gruvin/gruvin9x/wiki/Recognition.md

# Financial Contributors / Donators #

A number of people have contributed financially to the gruvin9x project by way of cash donations, consignment stock cost assistance and more.

The table below lists the first names (or initials) and country of financial contributors to date, in approximate chronological order.

## The gruvin9x Hall of (Financial) Recognition ##

| **Name** | **Country** |
|:---|:---|
| Keith | New Zealand |
| Cameron | United Kingdom |
| Jim | United States |
| Leo | Switzerland |
| Romolo | Italy |
| Brano | Canada |
| James | Canada |
| Rick | CA, USA |
| Tad L | MI, USA |

Many others have contributed their time or simply spread the word to the friends and colleagues, including many we have never heard from directly. To each and every one of you, please accept this token note of gratitude.
