gruvin/gruvin9x/wiki/About.attach/g9x-open-power.gif

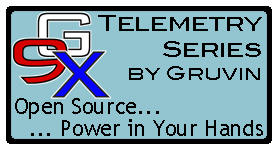
wiki/About.attach/g9x-open-power.gif
