gruvin/gruvin9x/wiki/About.attach/gruvin9x-lcd.jpg

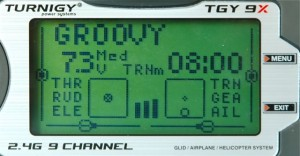
wiki/About.attach/gruvin9x-lcd.jpg
