gruvin/gruvin9x/wiki/Features.attach/drexpo_01.png

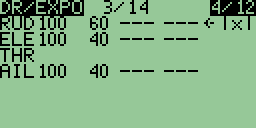
wiki/Features.attach/drexpo_01.png
