gruvin/gruvin9x/wiki/Features.attach/drexpo_02.png

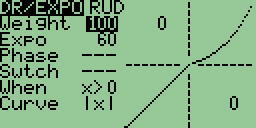
wiki/Features.attach/drexpo_02.png
