gruvin/gruvin9x/wiki/Features.attach/drexpo_04.png

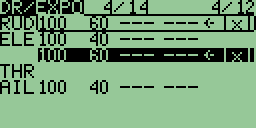
wiki/Features.attach/drexpo_04.png
