gruvin/gruvin9x/wiki/Features.attach/flightphases_01.png

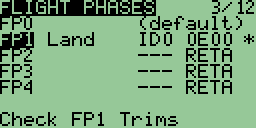
wiki/Features.attach/flightphases_01.png
