gruvin/gruvin9x/wiki/Features.attach/mainscreen_01.jpg

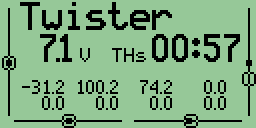
wiki/Features.attach/mainscreen_01.jpg
