gruvin/gruvin9x/wiki/Features.attach/mainscreen_02.jpg

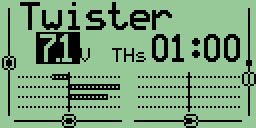
wiki/Features.attach/mainscreen_02.jpg
