gruvin/gruvin9x/wiki/Features.attach/mainscreen_04.jpg

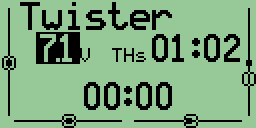
wiki/Features.attach/mainscreen_04.jpg
