gruvin/gruvin9x/wiki/Features.attach/modelsel_01.png

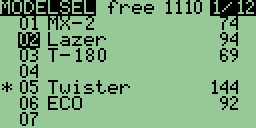
wiki/Features.attach/modelsel_01.png
