gruvin/gruvin9x/wiki/Features.attach/modelsel_02.png

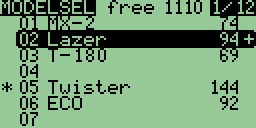
wiki/Features.attach/modelsel_02.png
