gruvin/gruvin9x/wiki/Features.attach/snapshot_01.png

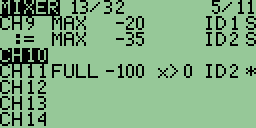
wiki/Features.attach/snapshot_01.png
