gruvin/gruvin9x/wiki/FrSky.attach/no-data-ani.gif

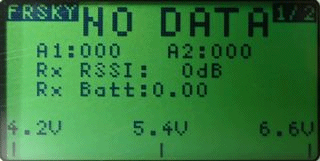
wiki/FrSky.attach/no-data-ani.gif
