gruvin/gruvin9x/wiki/PCB.attach/pcb_v3.2_3d_top.png

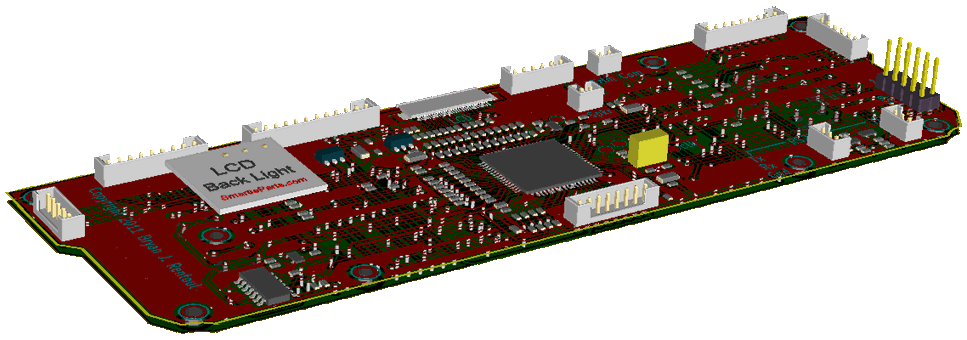
wiki/PCB.attach/pcb_v3.2_3d_top.png
