gruvin/gruvin9x/wiki/Progress.attach/FrSky RX Voltage.jpg

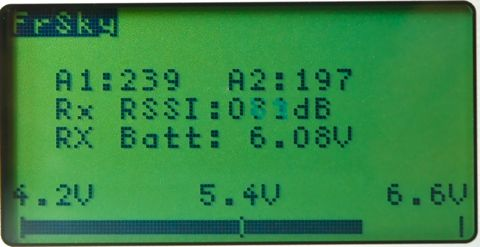
wiki/Progress.attach/FrSky RX Voltage.jpg
