gruvin/gruvin9x/archive/pcb-v4.1a-frozen/assembly/9xLABEL.pdf

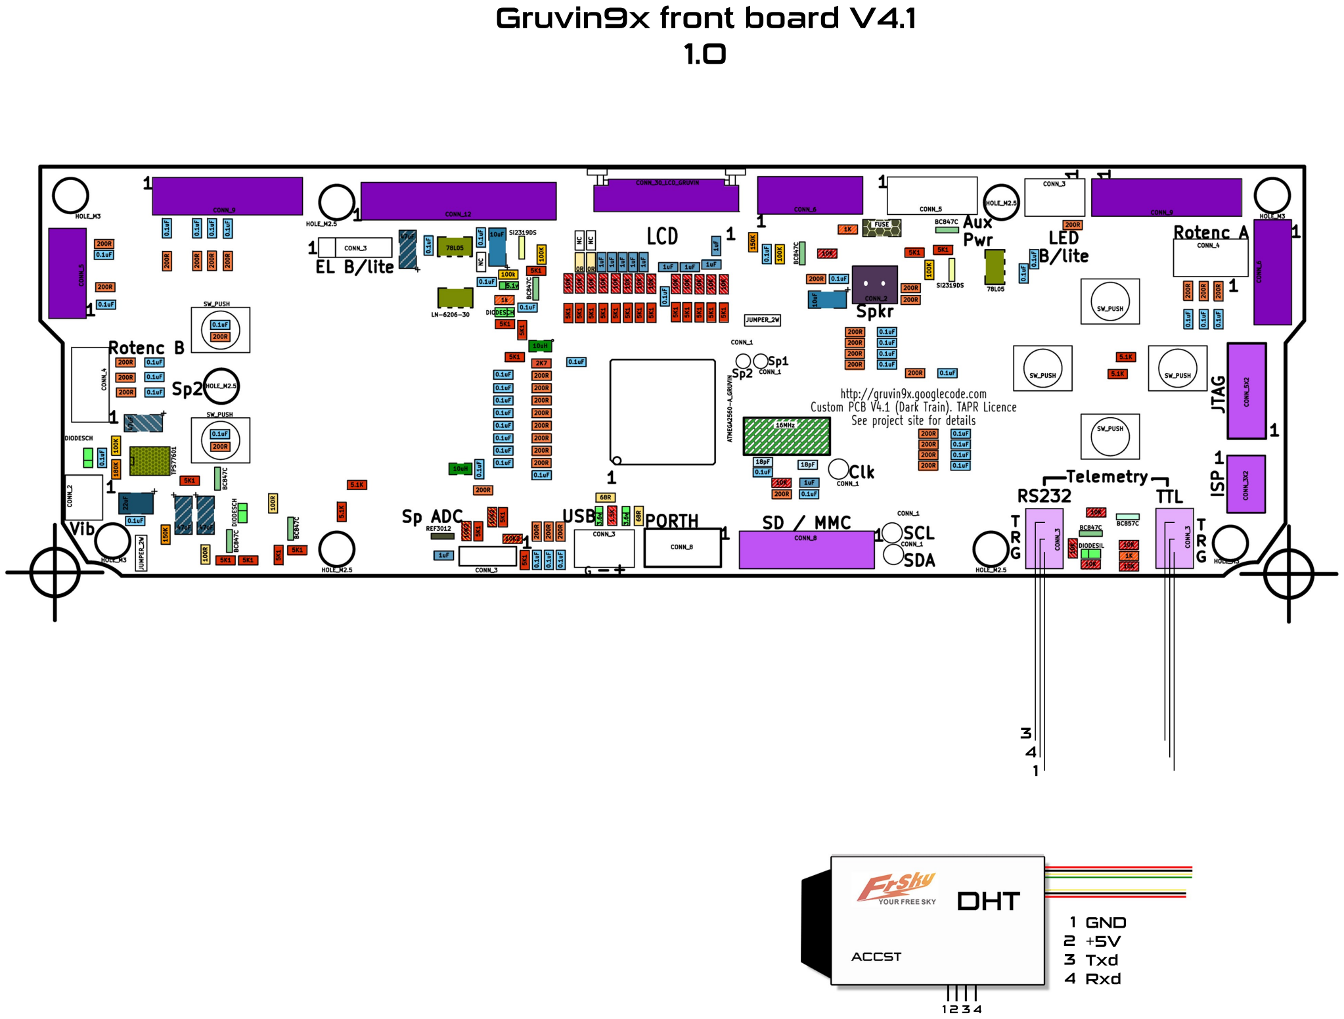
[picture p96: page 1]

Gruvin9x front board V4.1
1.0

1 2 3 4

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
