gruvin/gruvin9x/wiki/V41FAQ.attach/rot-enc-inside1.jpg

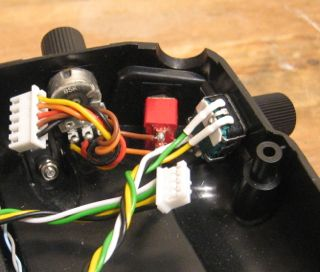
wiki/V41FAQ.attach/rot-enc-inside1.jpg
