gruvin/gruvin9x/archive/pcb-v4.1a-frozen/assembly/gruvin9x-SilkS_Front.pdf

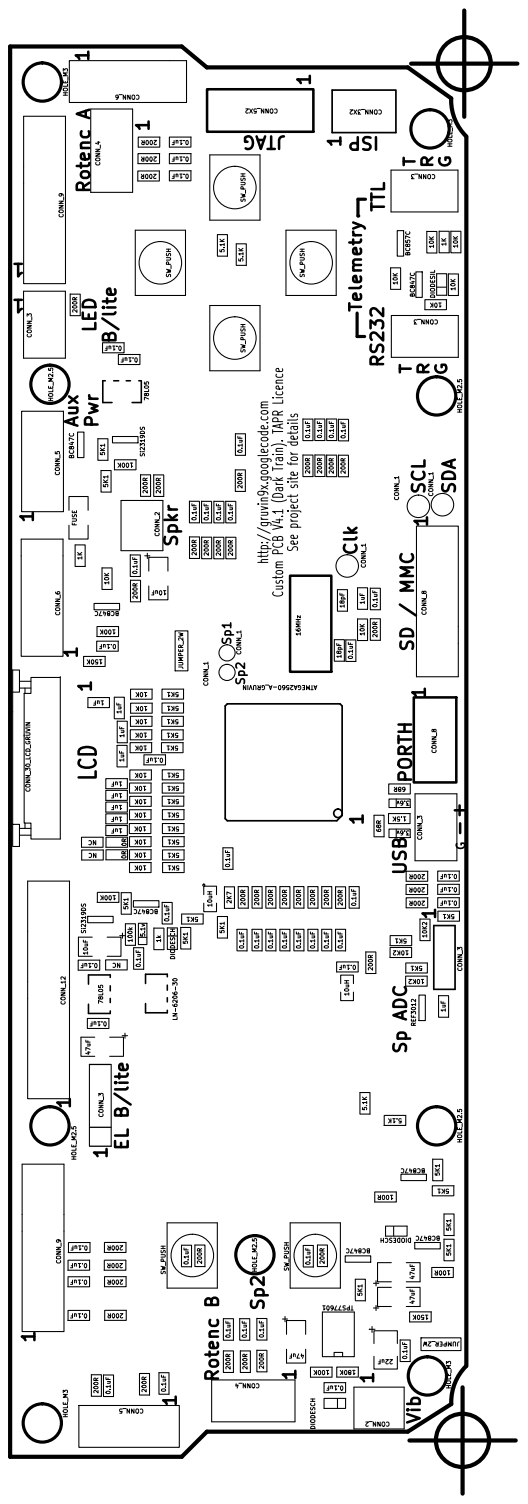
[picture p111: page 1]
