gruvin/gruvin9x/archive/pcb-v4.2-frozen/assembly/gruvin9x-v4.2-part-placement.pdf

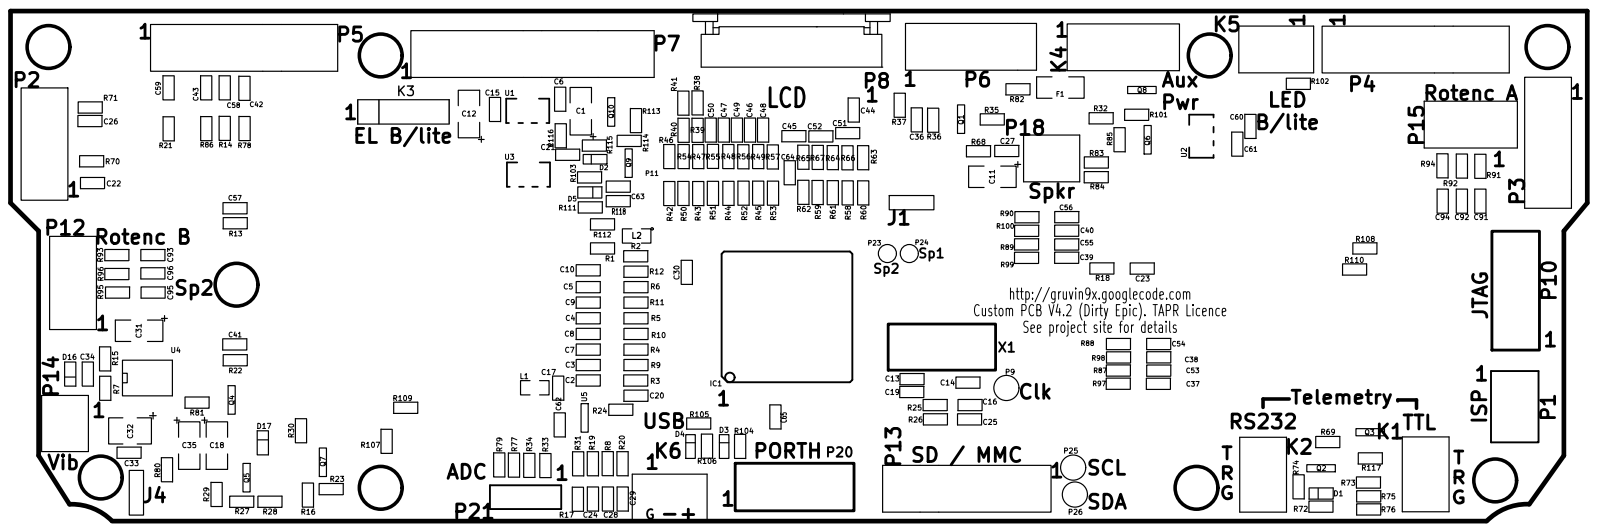
[picture p112: page 1]
