gruvin/gruvin9x/archive/pcb-v4.2-frozen/assembly/gruvin9x-v4.2-schematic.pdf

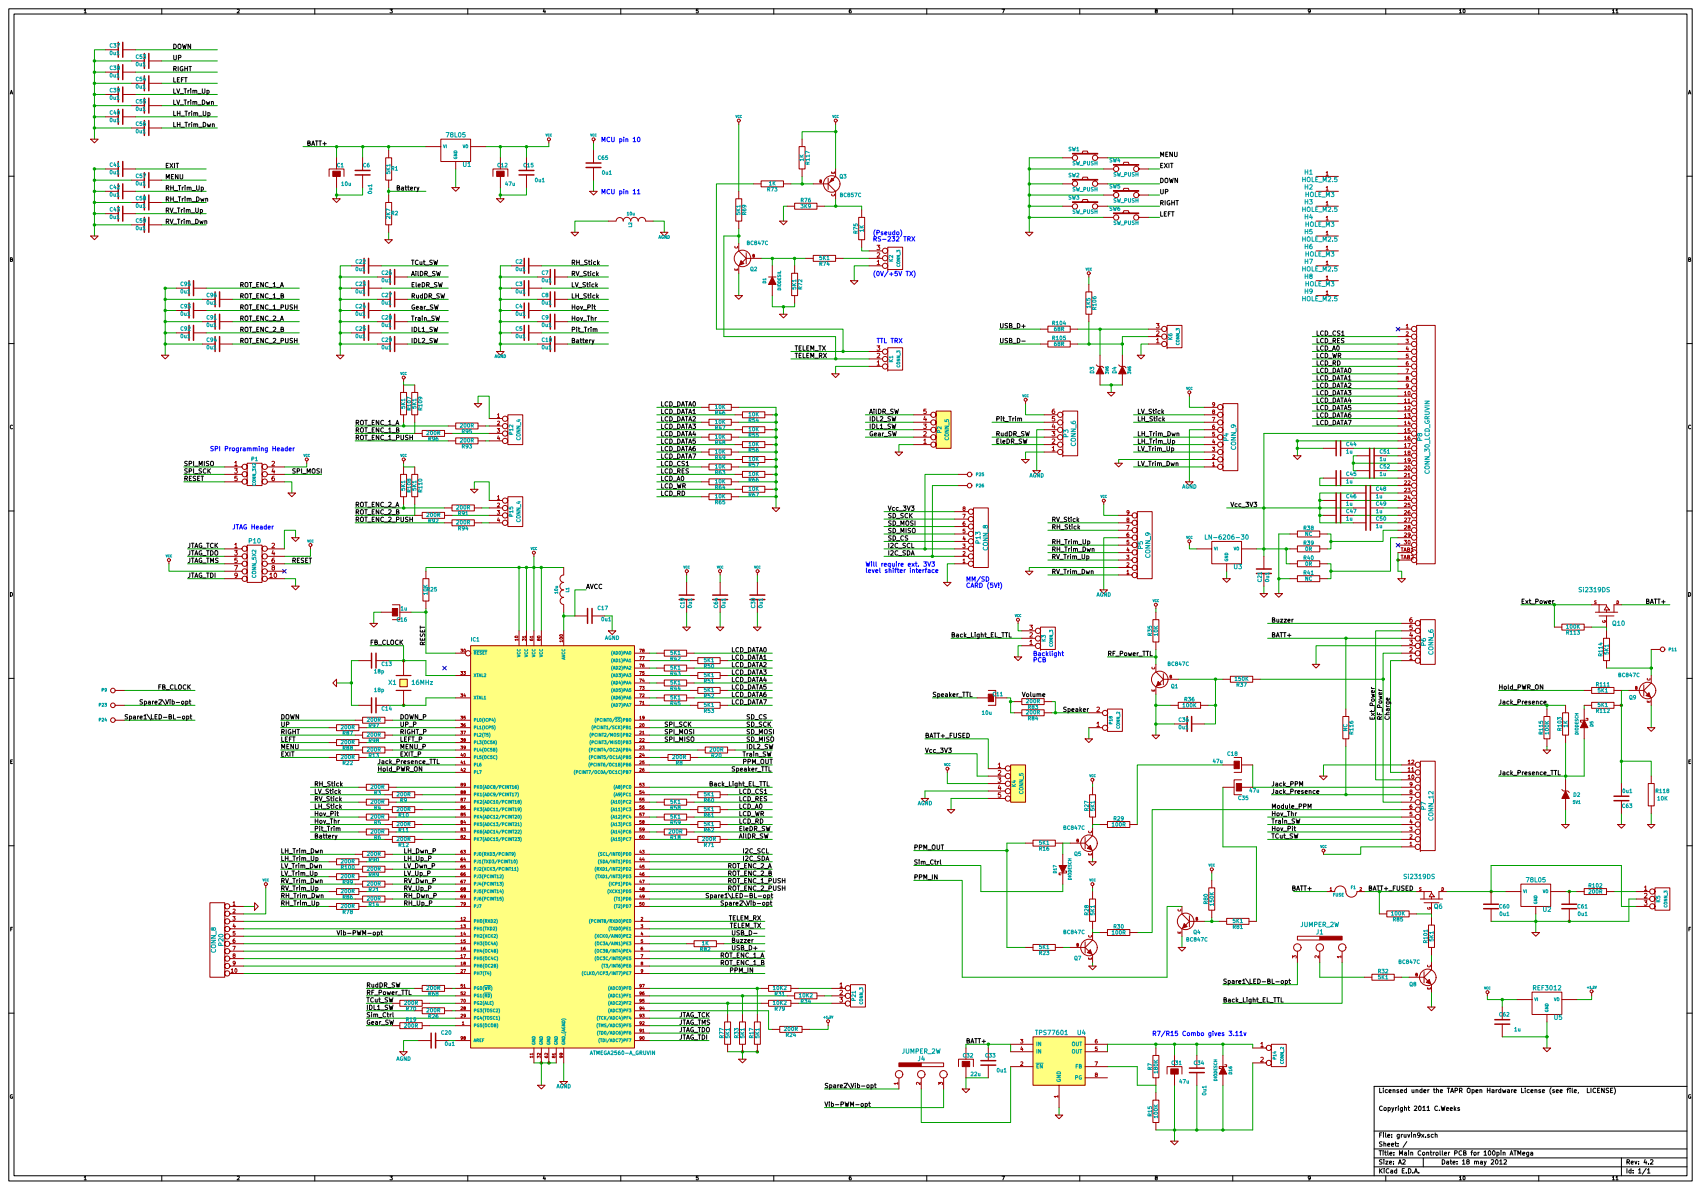
[picture p113: page 1]
