gruvin/gruvin9x/archive/pcb-v4.1a-frozen/assembly/sdcard_uk-SilkS_Front.pdf

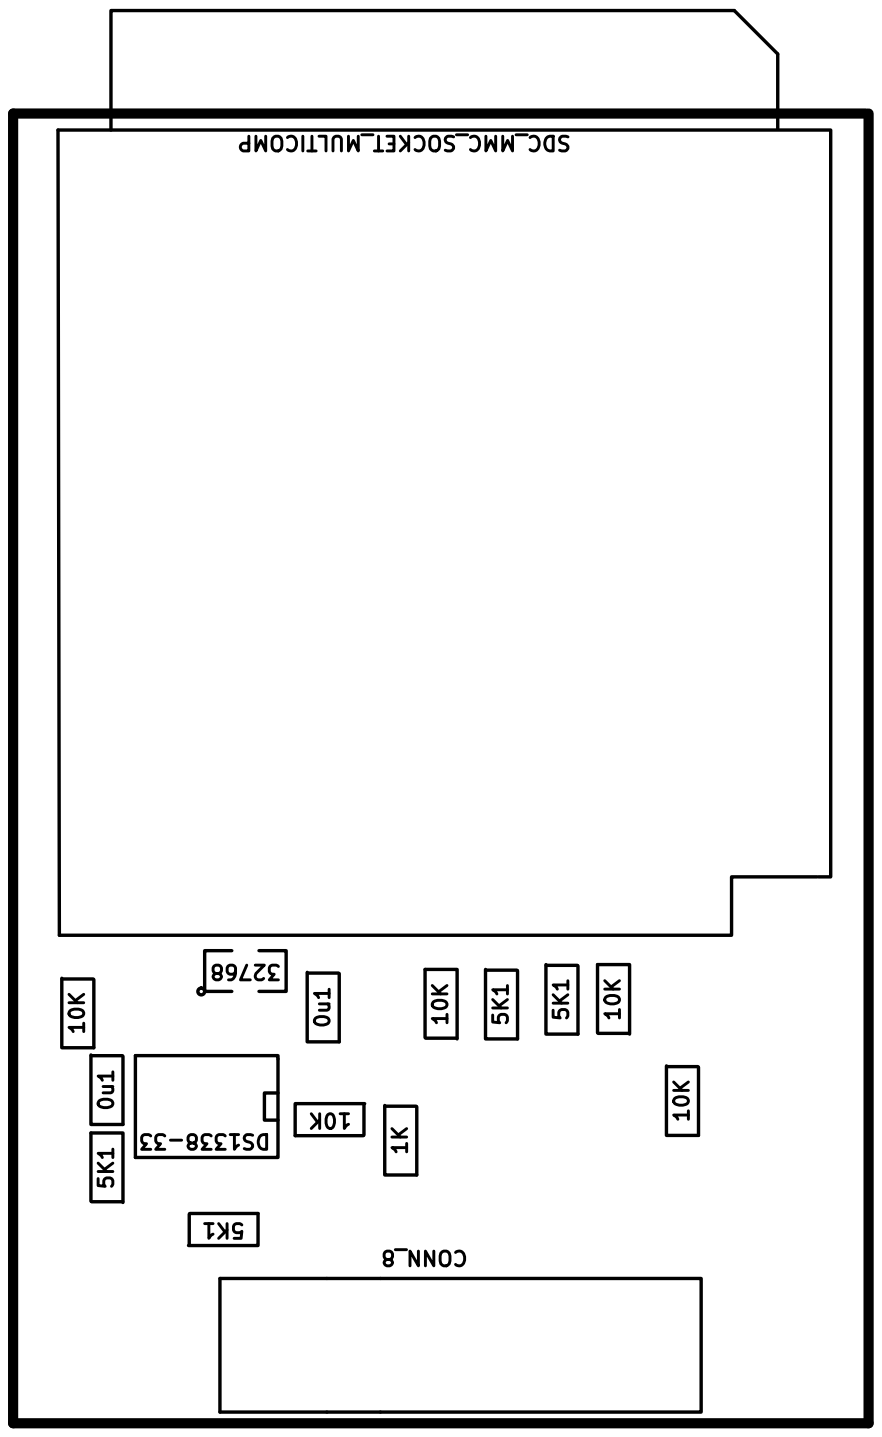
[picture p114: page 1]
