gruvin/gruvin9x/archive/pcb-v4.0-frozen/assembly/gruvin9x-SilkS_Front.pdf

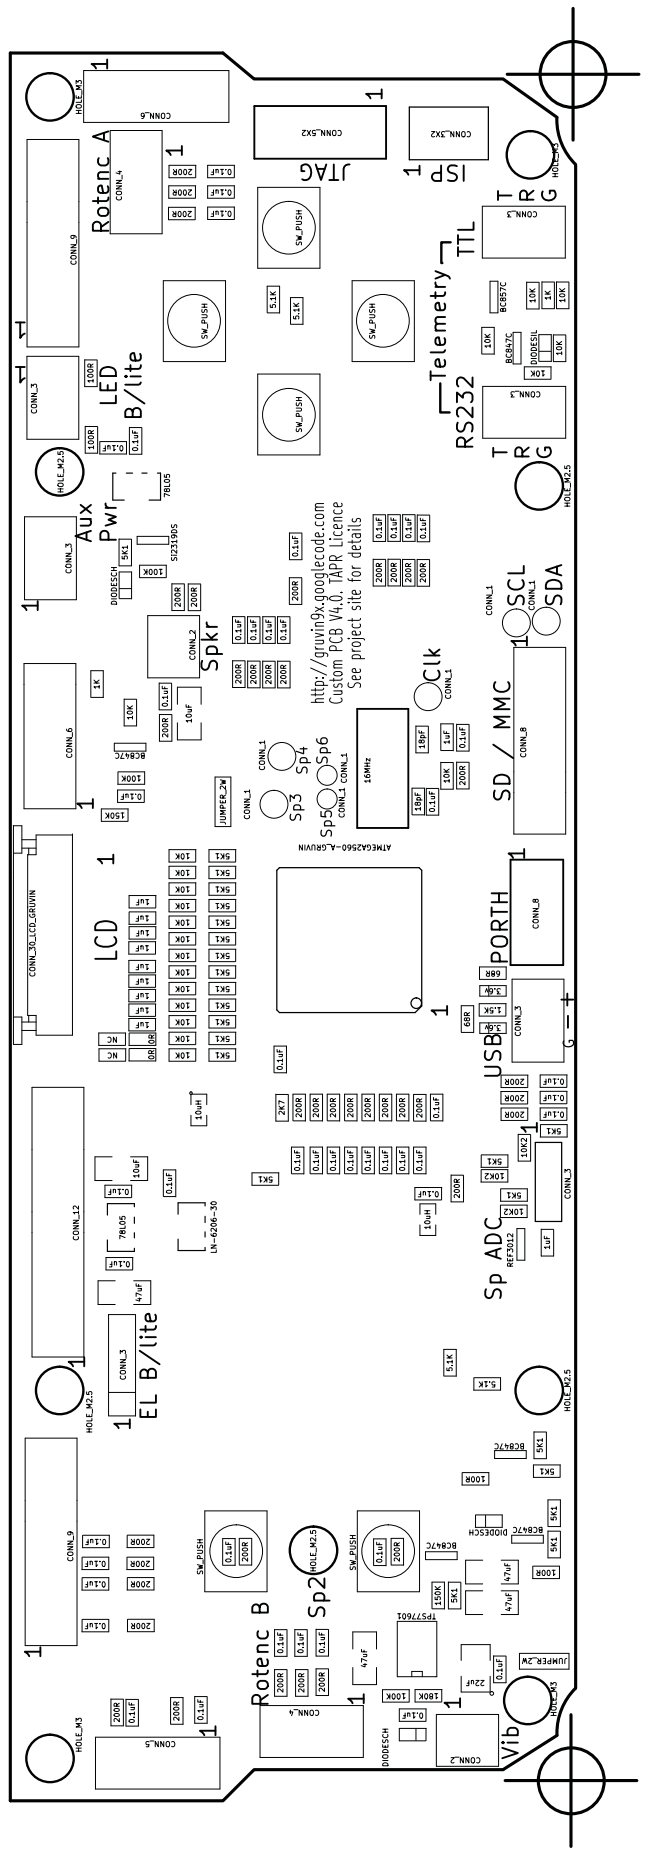
[picture p115: page 1]
