gruvin/gruvin9x/archive/pcb-v4.1a-frozen/assembly/sdcard-SilkS_Front.pdf

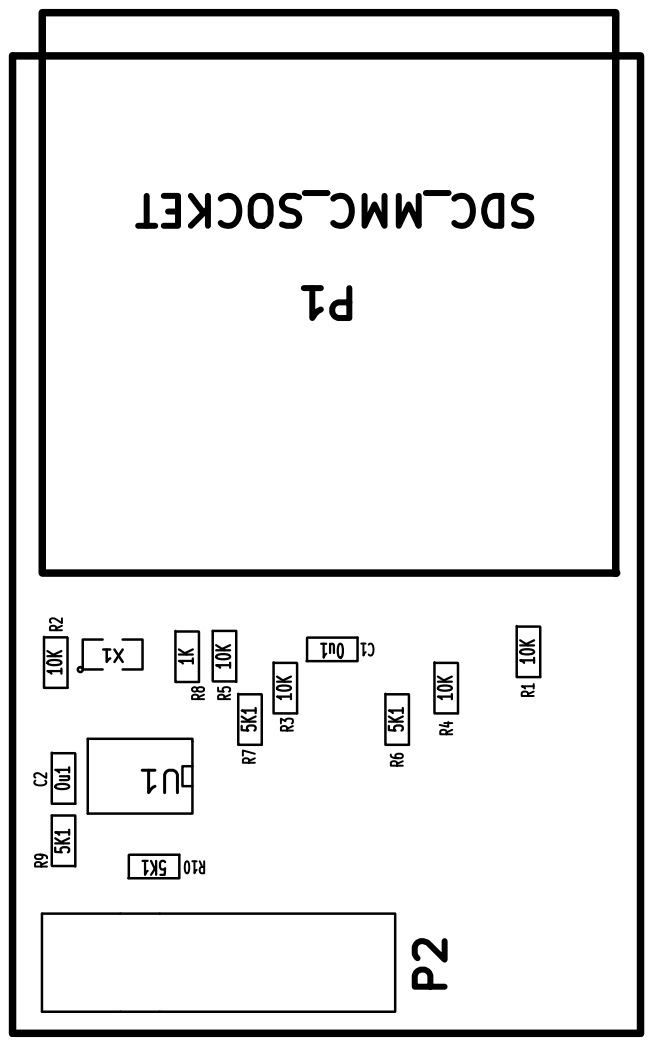
[picture p116: page 1]
