gruvin/gruvin9x/archive/pcb-v3.2-frozen/gruvin9x.pdf

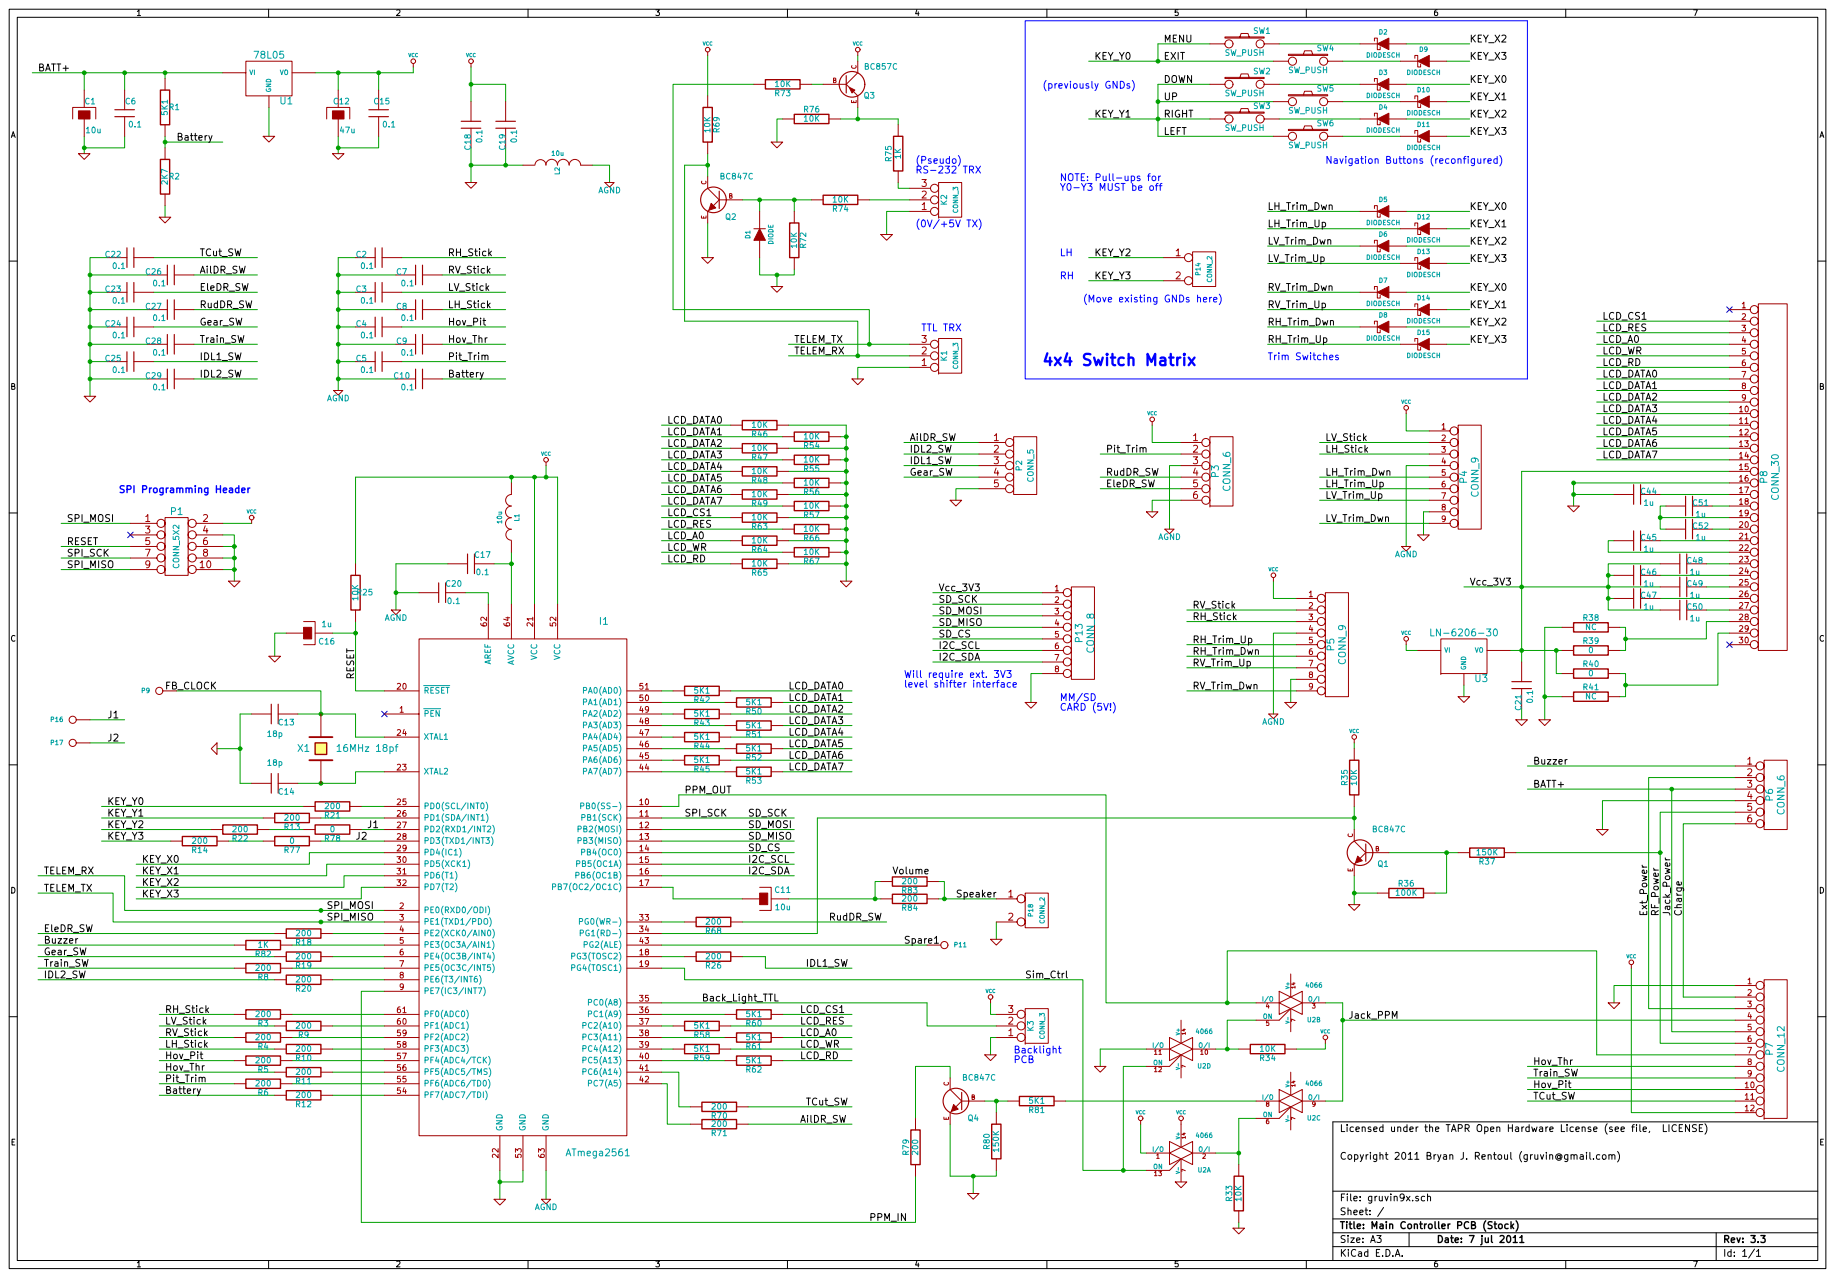
[picture p117: page 1]
