gruvin/gruvin9x/archive/pcb-v3.2-frozen/sdcard.pdf

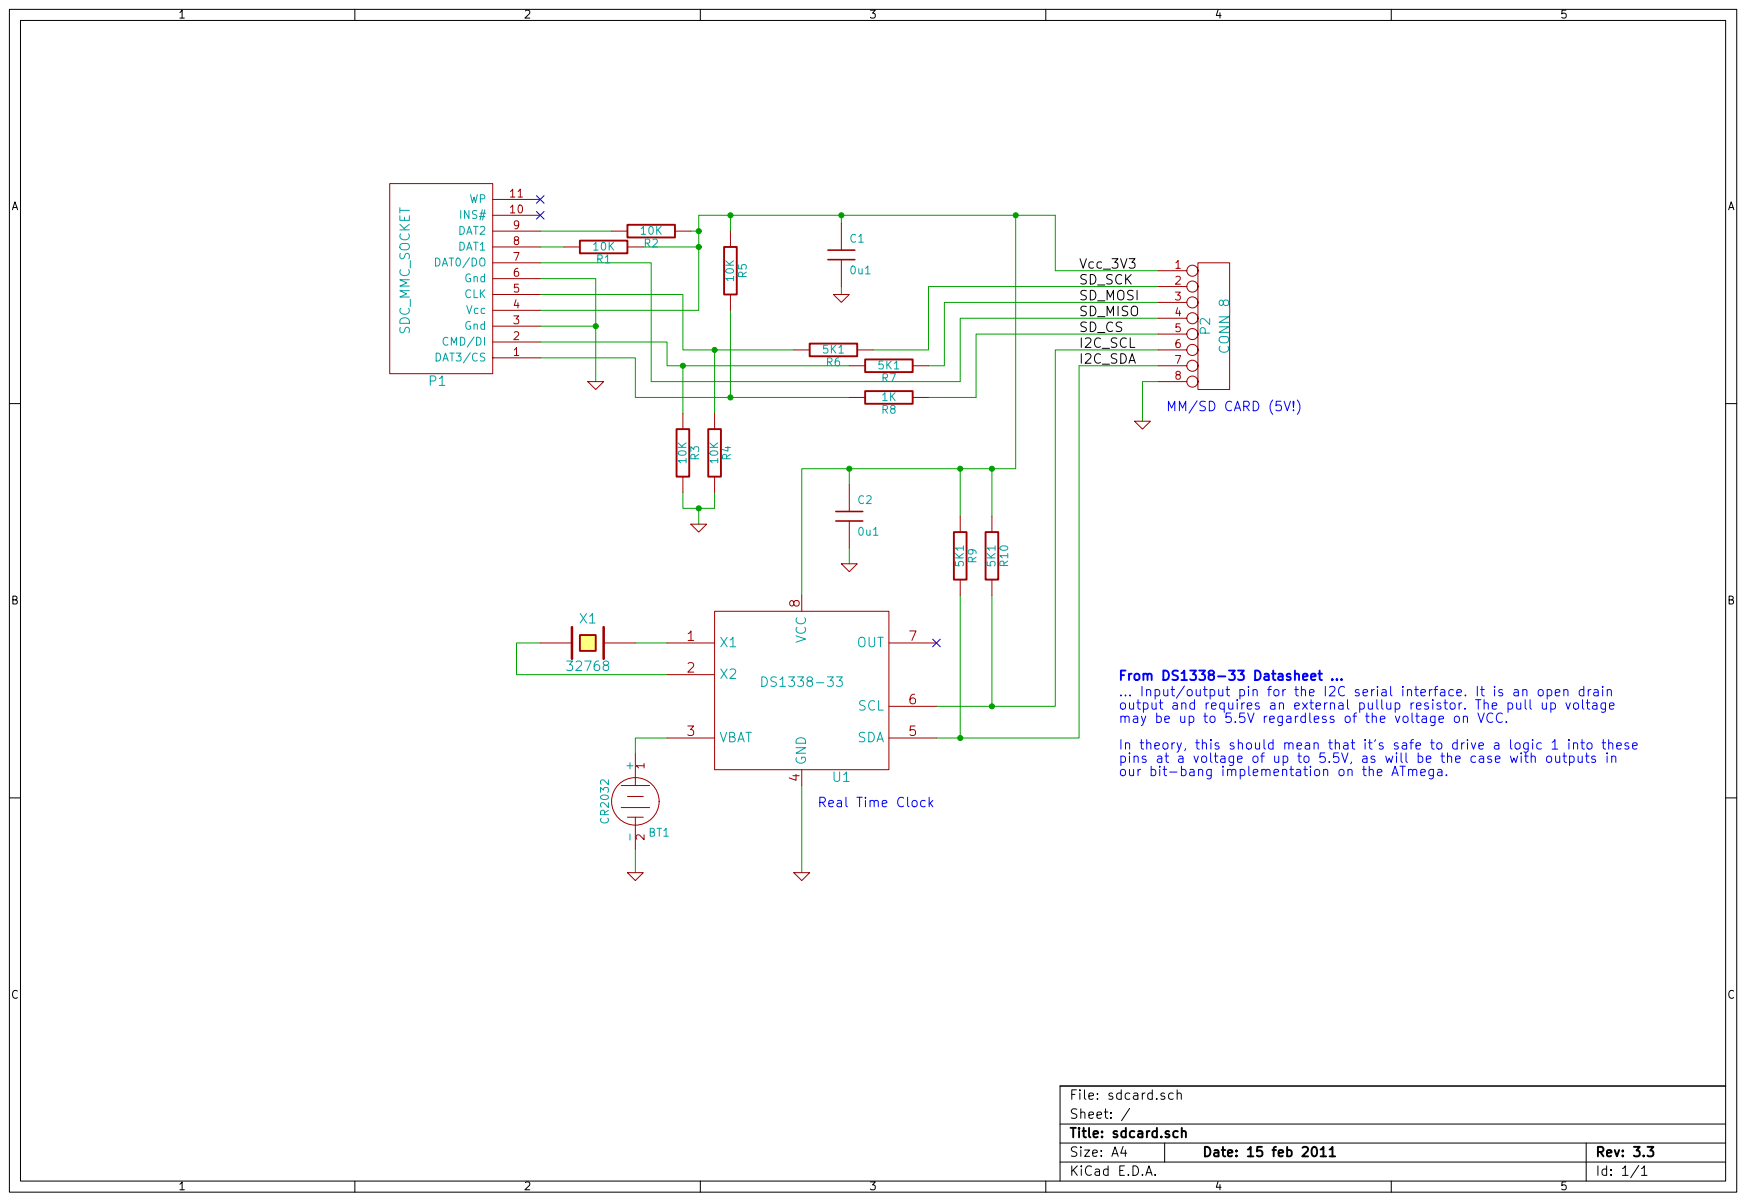
[picture p118: page 1]
