gruvin/gruvin9x/archive/pcb-v2.14-frozen/gruvin9x.pdf

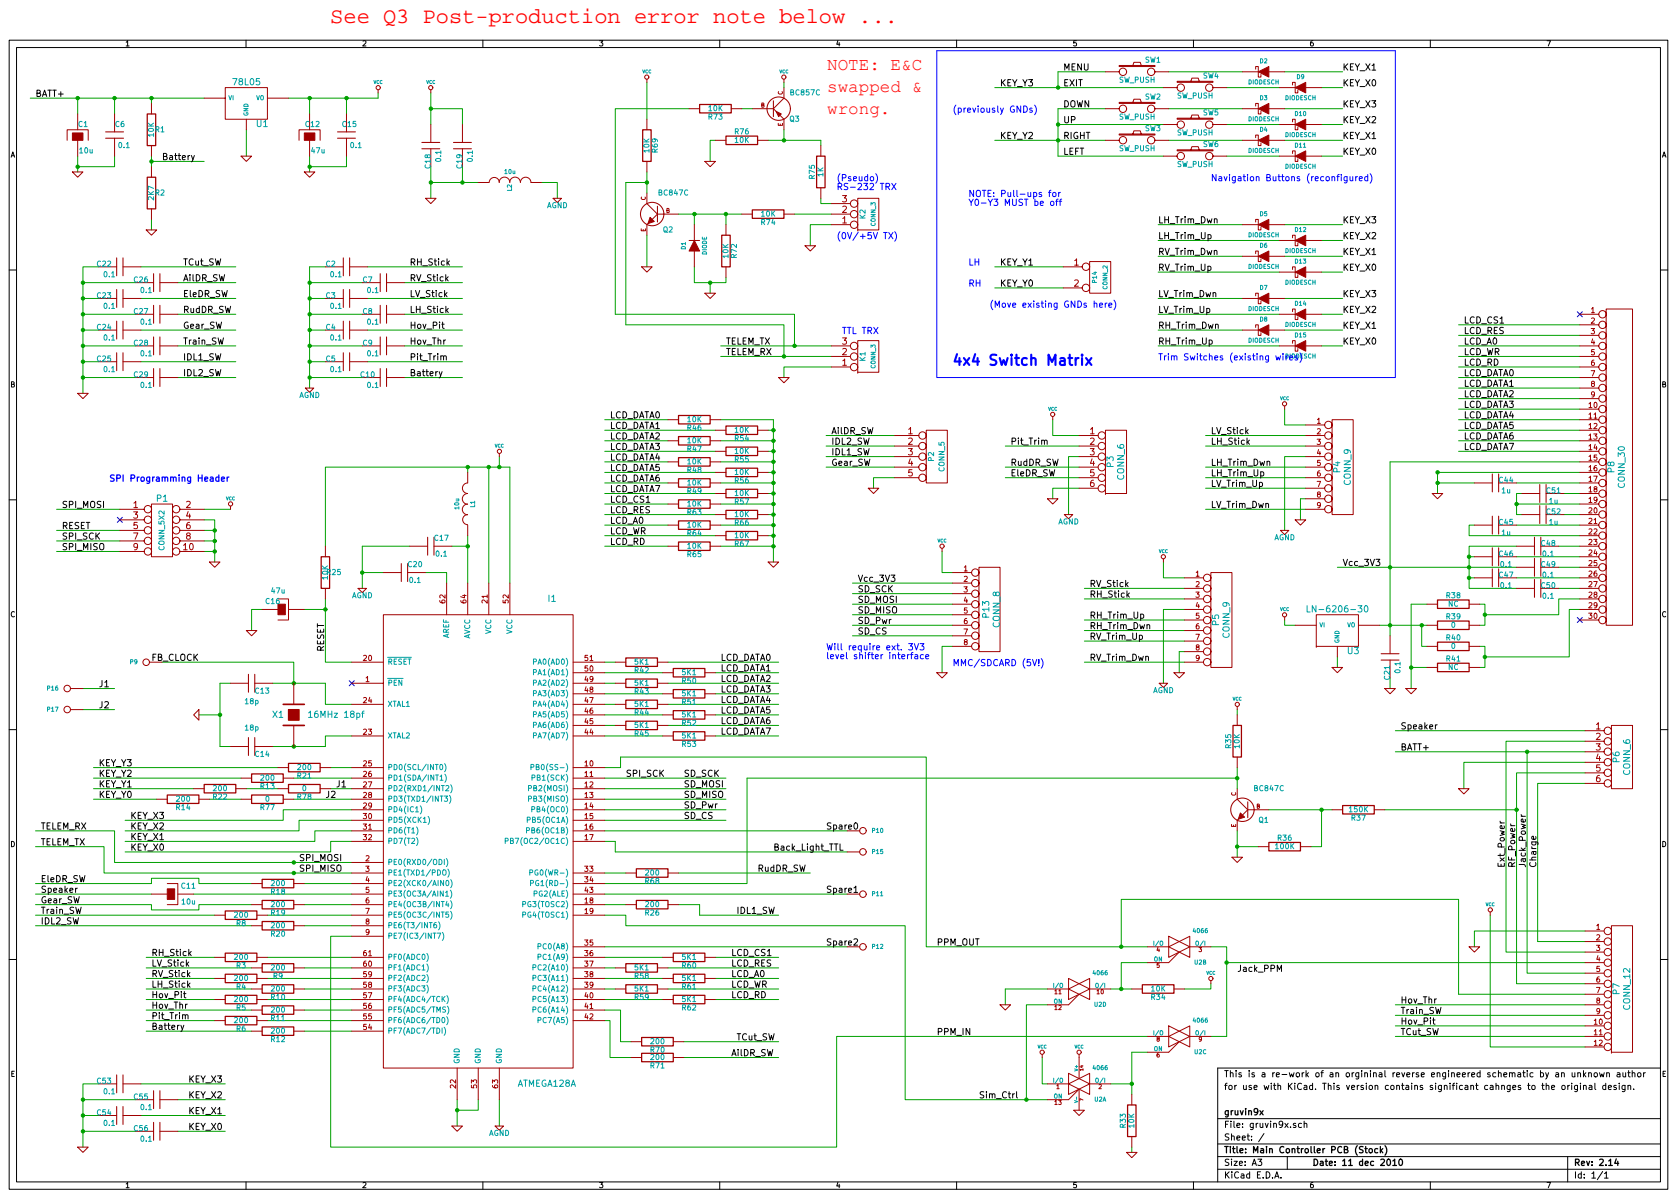
[picture p119: page 1]
