gruvin/gruvin9x/wiki/PCB.attach/gruvin9x-hacked.sch

## KiCad design wiki/PCB.attach/gruvin9x-hacked.sch (2015-06-02)

Schematic: gruvin9x-hacked.sch

Parts:
C1, C11: 10u
C2, C3, C4, C5, C6, C7, C8, C9, C10, C15, C17, C18, C19, C20, C21, C22, C23, C24, C25, C26, C27, C28, C29, C30, C31, C32, C33, C34, C35, C36, C37, C38, C39, C40, C41, C42, C43, C46, C47, C48, C49, C50: 0.1
C12, C16: 47u
C13, C14: 30p
C44, C45, C51, C52: 1u
I1: ATMEGA64A; ATMEGA64_08
L1, L2: 10u
P1: CONN_5X2
P2: CONN_5
P3, P6: CONN_6
P4, P5: CONN_9
P7: CONN_12
P8: CONN_30
PX: CONN_3
Q1: 2SC9014; SOT23EBD
R1, R25, R33, R34, R35, R46, R47, R48, R49, R54, R55, R56, R57, R63, R64, R65, R66, R67: 10K
R2: 2K7
R3, R4, R5, R6, R8, R9, R10, R11, R12, R13, R14, R15, R16, R18, R19, R20, R21, R22, R23, R24, R27, R28, R29, R30, R31, R32: 200
R26: 220
R36: 100K
R37: 150K
R38, R41: NC
R39, R40, R68: 0
R42, R43, R44, R45, R50, R51, R52, R53, R58, R59, R60, R61, R62: 5K1
RH1: 200
SW1, SW2, SW3, SW4, SW5, SW6: SW_PUSH
U1: 78L05; SOT89
U2: 4066
U3: LN-6206-30
X1: 16MHz

Notes on the sheet:
HACK
RS-232 to TTL inverter/level-shifter built 'dead bug' style on spare space of the rear casing PCB.
RS-232 +/12V
R7 removed
R17 removed
INPUT: Fr-Sky RXD converted to TTL SIL3 hot-glued to main PCB
SPI Programming Header
Navigation Buttons
Trim Switches
