gruvin/gruvin9x/firmware/src/frsky.cpp

/*
 * Authors (alphabetical order)
 * - Bertrand Songis <bsongis@gmail.com>
 * - Bryan J. Rentoul (Gruvin) <gruvin@gmail.com>
 *
 * Original contributors
 * - Philip Moss Adapted first frsky functions from jeti.cpp code by
 * - Karl Szmutny <shadow@privy.de>

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
 */

#ifdef SIMU
#include <math.h>
#endif
#include "gruvin9x.h"

// Enumerate FrSky packet codes
#define LINKPKT         0xfe
#define USRPKT          0xfd
#define A11PKT          0xfc
#define A12PKT          0xfb
#define A21PKT          0xfa
#define A22PKT          0xf9
#define ALRM_REQUEST    0xf8
#define RSSI1PKT        0xf7
#define RSSI2PKT        0xf6

#define START_STOP      0x7e
#define BYTESTUFF       0x7d
#define STUFF_MASK      0x20

uint8_t frskyRxBuffer[FRSKY_RX_PACKET_SIZE];   // Receive buffer. 9 bytes (full packet), worst case 18 bytes with byte-stuffing (+1)
uint8_t frskyTxBuffer[FRSKY_TX_PACKET_SIZE];   // Ditto for transmit buffer
uint8_t frskyTxBufferCount = 0;
uint8_t FrskyRxBufferReady = 0;
uint8_t frskyStreaming = 0;
uint8_t frskyUsrStreaming = 0;

uint16_t frskyComputeVolts(uint8_t rawADC, uint16_t ratio/* max cirecuit designed input voltage */, uint8_t decimals/* 1 or 2. defaults to 1 */)
{
  uint16_t val;
  val = (uint32_t)rawADC * ratio / ((decimals == 2) ? 255 : 2550); // result is naturally rounded and will in fact always be <= 16 bits
  return val;
}

/*
   Displays either a voltage or raw formatted value, given raw ADC, calibrartion ratio and optionally type, print mode and decimals
   type defaults to 0 -- volts
   mode defaults to 0 -- no special display attributes
   decimals can be either 1 or 2 and defaults to 1
  */
void frskyPutAValue(uint8_t x, uint8_t y, uint8_t channel, uint8_t value, uint8_t mode)
{
  if (g_model.frsky.channels[channel].type == 0/*volts*/)
  {
    uint16_t val = frskyComputeVolts(value, g_model.frsky.channels[channel].ratio, (mode & PREC2) ? 2 : 1);
    lcd_outdezNAtt(x, y, val, mode | (mode&PREC2 ? PREC2 : PREC1));
    lcd_putcAtt(lcd_lastPos, y, 'v', mode);
  }
  else /* assume raw */
  {
    lcd_outdezNAtt(x, y, value, mode&(~(PREC1|PREC2)), 3|LEADING0);
  }
}

FrskyData frskyTelemetry[2];
FrskyData frskyRSSI[2];

struct FrskyAlarm {
  uint8_t level;    // The alarm's 'urgency' level. 0=disabled, 1=yellow, 2=orange, 3=red
  uint8_t greater;  // 1 = 'if greater than'. 0 = 'if less than'
  uint8_t value;    // The threshold above or below which the alarm will sound
};

struct FrskyAlarm frskyAlarms[4];

#if defined(FRSKY_HUB) || defined(WS_HOW_HIGH)
FrskyHubData frskyHubData;
int16_t baroAltitudeOffset = 0;
#endif

void frskyPushValue(uint8_t *&ptr, uint8_t value)
{
  // byte stuff the only byte than might need it
  if (value == START_STOP) {
    *ptr++ = 0x5e;
    *ptr++ = BYTESTUFF;
  }
  else if (value == BYTESTUFF) {
    *ptr++ = 0x5d;
    *ptr++ = BYTESTUFF;
  }
  else {
    *ptr++ = value;
  }
}

#ifdef DISPLAY_USER_DATA
/*
  Copies all available bytes (up to max bufsize) from frskyUserData circular 
  buffer into supplied *buffer. Returns number of bytes copied (or zero)
*/
uint8_t frskyGetUserData(char *buffer, uint8_t bufSize)
{
  uint8_t i = 0;
  while (!frskyUserData.isEmpty())
  {
    buffer[i] = frskyUserData.get();
    i++;
  }
  return i;
}
#endif

#ifdef FRSKY_HUB
int8_t parseTelemHubIndex(uint8_t index)
{
  if (index > 0x26)
    index = 0; // invalid index
  if (index > 0x21)
    index -= 5;
  if (index > 0x0f)
    index -= 6;
  if (index > 0x08)
    index -= 2;
  return 2*(index-1);
}

typedef enum {
  TS_IDLE = 0,  // waiting for 0x5e frame marker
  TS_DATA_ID,   // waiting for dataID
  TS_DATA_LOW,  // waiting for data low byte
  TS_DATA_HIGH, // waiting for data high byte
  TS_XOR = 0x80 // decode stuffed byte
} TS_STATE;

void parseTelemHubByte(uint8_t byte)
{
  static int8_t structPos;
  static TS_STATE state = TS_IDLE;

  if (byte == 0x5e) {
    state = TS_DATA_ID;
    return;
  }
  if (state == TS_IDLE) {
    return;
  }
  if (state & TS_XOR) {
    byte = byte ^ 0x60;
    state = (TS_STATE)(state - TS_XOR);
  }
  if (byte == 0x5d) {
    state = (TS_STATE)(state | TS_XOR);
    return;
  }
  if (state == TS_DATA_ID) {
    structPos = parseTelemHubIndex(byte);
    state = TS_DATA_LOW;
    if (structPos < 0)
      state = TS_IDLE;
    return;
  }
  if (state == TS_DATA_LOW) {
    ((uint8_t*)&frskyHubData)[structPos] = byte;
    state = TS_DATA_HIGH;
    return;
  }
  ((uint8_t*)&frskyHubData)[structPos+1] = byte;
  state = TS_IDLE;
}
#endif

#ifdef WS_HOW_HIGH
void parseTelemWSHowHighByte(uint8_t byte)
{
  if (frskyUsrStreaming < (FRSKY_TIMEOUT10ms*3 - 10))  // At least 100mS passed since last data received
    ((uint8_t*)&frskyHubData)[offsetof(FrskyHubData, baroAltitude)] = byte;
  else
    ((uint8_t*)&frskyHubData)[offsetof(FrskyHubData, baroAltitude)+1] = byte;
  frskyUsrStreaming = FRSKY_TIMEOUT10ms*3; // reset counter
}
#endif  

/*
   Called from somewhere in the main loop or a low priority interrupt
   routine perhaps. This function processes FrSky telemetry data packets
   assembled by he USART0_RX_vect) ISR function (below) and stores
   extracted data in global variables for use by other parts of the program.

   Packets can be any of the following:

    - A1/A2/RSSI telemetry data
    - Alarm level/mode/threshold settings for Ch1A, Ch1B, Ch2A, Ch2B
    - User Data packets
*/

void processFrskyPacket(uint8_t *packet)
{
  // What type of packet?
  switch (packet[0])
  {
    case A22PKT:
    case A21PKT:
    case A12PKT:
    case A11PKT:
      {
        struct FrskyAlarm *alarmptr ;
        alarmptr = &frskyAlarms[(packet[0]-A22PKT)] ;
        alarmptr->value = packet[1];
        alarmptr->greater = packet[2] & 0x01;
        alarmptr->level = packet[3] & 0x03;
      }
      break;
    case LINKPKT: // A1/A2/RSSI values
      frskyTelemetry[0].set(packet[1]);
      frskyTelemetry[1].set(packet[2]);
      frskyRSSI[0].set(packet[3]);
      frskyRSSI[1].set(packet[4] / 2);
      break;

#if defined(FRSKY_HUB) || defined (WS_HOW_HIGH)
    case USRPKT: // User Data packet
      uint8_t numBytes = 3 + (packet[1] & 0x07); // sanitize in case of data corruption leading to buffer overflow
      for (uint8_t i=3; i<numBytes; i++) {
#if defined(FRSKY_HUB)
        if (g_model.frsky.usrProto == 1) // FrSky Hub
          parseTelemHubByte(packet[i]);
#endif
#if defined(WS_HOW_HIGH)
        if (g_model.frsky.usrProto == 2) // WS How High
          parseTelemWSHowHighByte(packet[i]);
#endif
      }
      break;
#endif
  }

  FrskyRxBufferReady = 0;
  frskyStreaming = FRSKY_TIMEOUT10ms; // reset counter only if valid frsky packets are being detected
}

// Receive buffer state machine state defs
#define frskyDataIdle    0
#define frskyDataStart   1
#define frskyDataInFrame 2
#define frskyDataXOR     3
/*
   Receive serial (RS-232) characters, detecting and storing each Fr-Sky 
   0x7e-framed packet as it arrives.  When a complete packet has been 
   received, process its data into storage variables.  NOTE: This is an 
   interrupt routine and should not get too lengthy. I originally had
   the buffer being checked in the perMain function (because per10ms
   isn't quite often enough for data streaming at 9600baud) but alas
   that scheme lost packets also. So each packet is parsed as it arrives,
   directly at the ISR function (through a call to frskyProcessPacket).
   
   If this proves a problem in the future, then I'll just have to implement
   a second buffer to receive data while one buffer is being processed (slowly).
*/

#ifndef SIMU
ISR(USART0_RX_vect)
{
  uint8_t stat;
  uint8_t data;
  
  static uint8_t numPktBytes = 0;
  static uint8_t dataState = frskyDataIdle;
  
  UCSR0B &= ~(1 << RXCIE0); // disable Interrupt
  sei() ;

  stat = UCSR0A; // USART control and Status Register 0 A

  /*
              bit      7      6      5      4      3      2      1      0
                      RxC0  TxC0  UDRE0    FE0   DOR0   UPE0   U2X0  MPCM0
             
              RxC0:   Receive complete
              TXC0:   Transmit Complete
              UDRE0:  USART Data Register Empty
              FE0:    Frame Error
              DOR0:   Data OverRun
              UPE0:   USART Parity Error
              U2X0:   Double Tx Speed
              PCM0:   MultiProcessor Comms Mode
   */
  // rh = UCSR0B; //USART control and Status Register 0 B

    /*
              bit      7      6      5      4      3      2      1      0
                   RXCIE0 TxCIE0 UDRIE0  RXEN0  TXEN0 UCSZ02  RXB80  TXB80
             
              RxCIE0:   Receive Complete int enable
              TXCIE0:   Transmit Complete int enable
              UDRIE0:   USART Data Register Empty int enable
              RXEN0:    Rx Enable
              TXEN0:    Tx Enable
              UCSZ02:   Character Size bit 2
              RXB80:    Rx data bit 8
              TXB80:    Tx data bit 8
    */

  data = UDR0; // USART data register 0

  if (stat & ((1 << FE0) | (1 << DOR0) | (1 << UPE0)))
  { // discard buffer and start fresh on any comms error
    FrskyRxBufferReady = 0;
    numPktBytes = 0;
  } 
  else
  {
    if (FrskyRxBufferReady == 0) // can't get more data if the buffer hasn't been cleared
    {
      switch (dataState) 
      {
        case frskyDataStart:
          if (data == START_STOP) break; // Remain in userDataStart if possible 0x7e,0x7e doublet found.

          if (numPktBytes < FRSKY_RX_PACKET_SIZE)
            frskyRxBuffer[numPktBytes++] = data;
          dataState = frskyDataInFrame;
          break;

        case frskyDataInFrame:
          if (data == BYTESTUFF)
          { 
              dataState = frskyDataXOR; // XOR next byte
              break; 
          }
          if (data == START_STOP) // end of frame detected
          {
            processFrskyPacket(frskyRxBuffer); // FrskyRxBufferReady = 1;
            dataState = frskyDataIdle;
            break;
          }
          if (numPktBytes < FRSKY_RX_PACKET_SIZE)
            frskyRxBuffer[numPktBytes++] = data;
          break;

        case frskyDataXOR:
          if (numPktBytes < FRSKY_RX_PACKET_SIZE)
            frskyRxBuffer[numPktBytes++] = data ^ STUFF_MASK;
          dataState = frskyDataInFrame;
          break;

        case frskyDataIdle:
          if (data == START_STOP)
          {
            numPktBytes = 0;
            dataState = frskyDataStart;
          }
          break;

      } // switch
    } // if (FrskyRxBufferReady == 0)
  }
  cli() ;
  UCSR0B |= (1 << RXCIE0); // enable Interrupt
}

#endif

/******************************************/

void frskyTransmitBuffer()
{
  UCSR0B |= (1 << UDRIE0); // enable  UDRE0 interrupt
}

uint8_t FrskyAlarmSendState = 0 ;
void FRSKY10mspoll(void)
{
  if (frskyTxBufferCount)
    return; // we only have one buffer. If it's in use, then we can't send yet.

  uint8_t *ptr = &frskyTxBuffer[0];

  *ptr++ = START_STOP;        // End of packet
  *ptr++ = 0x00;
  *ptr++ = 0x00;
  *ptr++ = 0x00;
  *ptr++ = 0x00;
  *ptr++ = 0x00;

  // Now send a packet
  FrskyAlarmSendState -= 1 ;
  uint8_t alarm = 1 - (FrskyAlarmSendState % 2);
  if (FrskyAlarmSendState < SEND_MODEL_ALARMS) {
    uint8_t channel = 1 - (FrskyAlarmSendState / 2);
    *ptr++ = ALARM_LEVEL(channel, alarm);
    *ptr++ = ALARM_GREATER(channel, alarm);
    frskyPushValue(ptr, g_model.frsky.channels[channel].alarms_value[alarm]);
    *ptr++ = (A22PKT + FrskyAlarmSendState); // fc - fb - fa - f9
  }

  *ptr++ = START_STOP;        // Start of packet

  frskyTxBufferCount = ptr - &frskyTxBuffer[0];
  frskyTransmitBuffer();
}

bool FRSKY_alarmRaised(uint8_t idx)
{
  for (int i=0; i<2; i++) {
    if (ALARM_LEVEL(idx, i) != alarm_off) {
      if (ALARM_GREATER(idx, i)) {
        if (frskyTelemetry[idx].value > g_model.frsky.channels[idx].alarms_value[i])
          return true;
      }
      else {
        if (frskyTelemetry[idx].value < g_model.frsky.channels[idx].alarms_value[i])
          return true;
      }
    }
  }
  return false;
}

inline void FRSKY_EnableTXD(void)
{
  frskyTxBufferCount = 0;
  UCSR0B |= (1 << TXEN0); // enable TX
}

inline void FRSKY_EnableRXD(void)
{
  UCSR0B |= (1 << RXEN0);  // enable RX
  UCSR0B |= (1 << RXCIE0); // enable Interrupt
}

void FRSKY_Init(void)
{
  // clear frsky variables
  memset(frskyAlarms, 0, sizeof(frskyAlarms));
  resetTelemetry();

  DDRE &= ~(1 << DDE0);    // set RXD0 pin as input
  PORTE &= ~(1 << PORTE0); // disable pullup on RXD0 pin

#undef BAUD
#define BAUD 9600
#ifndef SIMU
#include <util/setbaud.h>

  UBRR0H = UBRRH_VALUE;
  UBRR0L = UBRRL_VALUE;
  UCSR0A &= ~(1 << U2X0); // disable double speed operation.

  // set 8N1
  UCSR0B = 0 | (0 << RXCIE0) | (0 << TXCIE0) | (0 << UDRIE0) | (0 << RXEN0) | (0 << TXEN0) | (0 << UCSZ02);
  UCSR0C = 0 | (1 << UCSZ01) | (1 << UCSZ00);

  
  while (UCSR0A & (1 << RXC0)) UDR0; // flush receive buffer

#endif

  // These should be running right from power up on a FrSky enabled '9X.
  FRSKY_EnableTXD(); // enable FrSky-Telemetry command transmission
  FRSKY_EnableRXD(); // enable FrSky-Telemetry data reception
}

void FrskyData::set(uint8_t value)
{
   this->value = value;
   if (!max || max < value)
     max = value;
   if (!min || min > value)
     min = value;
}

void resetTelemetry()
{
  memset(frskyTelemetry, 0, sizeof(frskyTelemetry));
  memset(frskyRSSI, 0, sizeof(frskyRSSI));
#if defined(FRSKY_HUB) || defined(WS_HOW_HIGH)
  baroAltitudeOffset = -frskyHubData.baroAltitude;
#endif
}

inline double deg2rad(double deg)
{
  return (deg * 3.14159265 / 180);
}

// Haversine formula for short distances, reference http://andrew.hedges.name/experiments/haversine/
// Earth circumference reference, http://en.wikipedia.org/wiki/Great-circle_distance
// Math performed by MCU is within 2.8% of that performed by JavaScript in
// Firefox, on my Mac over a ~7,500m test distance.  GPS is not that accurate
// (by far) so I'm happy enough with the results here.
double distance(double lat1, double lon1, double lat2, double lon2)
{
  double dlon, dlat, a, c;
  dlon = deg2rad(lon2 - lon1);
  dlat = deg2rad(lat2 - lat1);
  a = pow(sin(dlat/2), 2) + cos(lat1) * cos(lat2) * pow(sin(dlon/2), 2);
  c = 2 * atan2( sqrt(a), sqrt(1-a) );  // great circle distance in radians
  return (6372800 * c); // meters
}
