gruvin/gruvin9x/firmware/src/ffcc932.cpp

/*
 * Authors (alphabetical order)
 * - Bertrand Songis <bsongis@gmail.com>
 * - Bryan J. Rentoul (Gruvin) <gruvin@gmail.com>
 *
 * gruvin9x is based on code named er9x by
 * Author - Erez Raviv <erezraviv@gmail.com>, which is in turn
 * was based on the original (and ongoing) project by Thomas Husterer,
 * th9x -- http://code.google.com/p/th9x/
 *
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
 */

/*------------------------------------------------------------------------*/
/* Unicode - OEM code bidirectional converter  (C)ChaN, 2009              */
/*                                                                        */
/* CP932 (Japanese Shift-JIS)                                             */
/*------------------------------------------------------------------------*/

#include "ff.h"

#define _TINY_TABLE	0

#if !_USE_LFN || _CODE_PAGE != 932
#error This file is not needed in current configuration. Remove from the project.
#endif


static
const WCHAR uni2sjis[] = {
/*  Unicode - Sjis, Unicode - Sjis, Unicode - Sjis, Unicode - Sjis, */
	0x00A7, 0x8198, 0x00A8, 0x814E, 0x00B0, 0x818B, 0x00B1, 0x817D,
	0x00B4, 0x814C, 0x00B6, 0x81F7, 0x00D7, 0x817E, 0x00F7, 0x8180,
	0x0391, 0x839F, 0x0392, 0x83A0, 0x0393, 0x83A1, 0x0394, 0x83A2,
	0x0395, 0x83A3, 0x0396, 0x83A4, 0x0397, 0x83A5, 0x0398, 0x83A6,
	0x0399, 0x83A7, 0x039A, 0x83A8, 0x039B, 0x83A9, 0x039C, 0x83AA,
	0x039D, 0x83AB, 0x039E, 0x83AC, 0x039F, 0x83AD, 0x03A0, 0x83AE,
	0x03A1, 0x83AF, 0x03A3, 0x83B0, 0x03A4, 0x83B1, 0x03A5, 0x83B2,
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
	0x8179, 0x3010, 0x817A, 0x3011, 0x817B, 0xFF0B, 0x817C, 0xFF0D,
	0x817D, 0x00B1, 0x817E, 0x00D7, 0x8180, 0x00F7, 0x8181, 0xFF1D,
	0x8182, 0x2260, 0x8183, 0xFF1C, 0x8184, 0xFF1E, 0x8185, 0x2266,
	0x8186, 0x2267, 0x8187, 0x221E, 0x8188, 0x2234, 0x8189, 0x2642,
	0x818A, 0x2640, 0x818B, 0x00B0, 0x818C, 0x2032, 0x818D, 0x2033,
	0x818E, 0x2103, 0x818F, 0xFFE5, 0x8190, 0xFF04, 0x8191, 0xFFE0,
	0x8192, 0xFFE1, 0x8193, 0xFF05, 0x8194, 0xFF03, 0x8195, 0xFF06,
	0x8196, 0xFF0A, 0x8197, 0xFF20, 0x8198, 0x00A7, 0x8199, 0x2606,
	0x819A, 0x2605, 0x819B, 0x25CB, 0x819C, 0x25CF, 0x819D, 0x25CE,
	0x819E, 0x25C7, 0x819F, 0x25C6, 0x81A0, 0x25A1, 0x81A1, 0x25A0,
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
};
#endif



WCHAR ff_convert (	/* Converted code, 0 means conversion error */
	WCHAR	src,	/* Character code to be converted */
	UINT	dir		/* 0: Unicode to OEMCP, 1: OEMCP to Unicode */
)
{
	const WCHAR *p;
	WCHAR c;
	int i, n, li, hi;


	if (src <= 0x80) {	/* ASCII */
		c = src;
	} else {
#if !_TINY_TABLE
		if (dir) {		/* OEMCP to unicode */
			p = sjis2uni;
			hi = sizeof(sjis2uni) / 4 - 1;
		} else {		/* Unicode to OEMCP */
			p = uni2sjis;
			hi = sizeof(uni2sjis) / 4 - 1;
		}
		li = 0;
		for (n = 16; n; n--) {
			i = li + (hi - li) / 2;
			if (src == p[i * 2]) break;
			if (src > p[i * 2])
				li = i;
			else
				hi = i;
		}
		c = n ? p[i * 2 + 1] : 0;
#else
		if (dir) {		/* OEMCP to unicode (Incremental search)*/
			p = &uni2sjis[1];
			do {
				c = *p;
				p += 2;
			} while (c && c != src);
			p -= 3;
			c = *p;
		} else {		/* Unicode to OEMCP */
			li = 0; hi = sizeof(uni2sjis) / 4 - 1;
			for (n = 16; n; n--) {
				i = li + (hi - li) / 2;
				if (src == uni2sjis[i * 2]) break;
				if (src > uni2sjis[i * 2])
					li = i;
				else
					hi = i;
			}
			c = n ? uni2sjis[i * 2 + 1] : 0;
		}
#endif
	}

	return c;
}



WCHAR ff_wtoupper (	/* Upper converted character */
	WCHAR chr		/* Input character */
)
{
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
	int i;


	for (i = 0; tbl_lower[i] && chr != tbl_lower[i]; i++) ;

	return tbl_lower[i] ? tbl_upper[i] : chr;
}
