gruvin/gruvin9x/firmware/src/logs.cpp

/*
 * Authors (alphabetical order)
 * - Bertrand Songis <bsongis@gmail.com>
 * - Bryan J. Rentoul (Gruvin) <gruvin@gmail.com>
 *
 * Original contributors
 * - Philip Moss Adapted first frsky functions from jeti.cpp code by
 * - Karl Szmutny <shadow@privy.de>

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
 */

#include "logs.h"

char g_logFilename[13]; // 8+dot+3+null
char g_logErrorStr[22] = { 0 };
int8_t g_telemLogState = 0;
FATFS g_FATFS_Obj;
FIL g_oLogFile;
char logFullPath[21]; 

// initTelemLog: Determine and set telemetry log filename
void initTelemLog() // pers.cpp -- after loading model data
{
  FRESULT result;

  // close any file left open. E.G. Changing models with log switch still on.
  if (g_oLogFile.fs) f_close(&g_oLogFile);
  g_telemLogState = 0;

  strcpy_P(g_logFilename, PSTR("M00_000.CSV")); // filename only.

  // Set log file model number
  uint8_t num = g_eeGeneral.currModel + 1;
  char *n = &g_logFilename[2];
  *n = (char)((num % 10) + '0');
  *(--n) = (char)((num / 10) + '0');

  // Loop, skipping over any existing log files ... _000, _001, etc. until we have a unique file name
  result = f_mount(0, &g_FATFS_Obj);
  if (result!=FR_OK)
  {
    strcpy_P(g_logErrorStr, PSTR("SDCARD F/S ERROR"));
    g_telemLogState = -result;
    return;
  }
  while (1)
  {
    strcpy(logFullPath, TELEM_LOG_PATH);
    strcat(logFullPath, "/");
    strcat(logFullPath, g_logFilename);

    result = f_open(&g_oLogFile, logFullPath, FA_OPEN_EXISTING | FA_READ);
    if (result == FR_OK)
    {
      f_close(&g_oLogFile);

      // bump log file counter NNN (Mxx_NNN.txt)
      n = &g_logFilename[6];
      if (++*n > '9')
      {
        *n='0';
        n--;
        if (++*n > '9')
        {
          *n='0';
          n--;
          if (++*n > '9')
          {
            *n='0';
            break; // Wow. We looped back around past 999 to 000! abort loop
          }
        }
      }
    }
    else if (result == FR_NO_FILE /*TODO check this code. What should happen here? */)
    {
      break;
    }
    else if (result == FR_NO_PATH)
    {
      if (f_mkdir(TELEM_LOG_PATH) != FR_OK)
      {
        strcpy_P(g_logErrorStr, PSTR("Check "));
        strcat(g_logErrorStr, TELEM_LOG_PATH);
        strcat(g_logErrorStr, PSTR(" folder"));
        g_telemLogState = -result;
        return;
      }
    }
    else
    {
      g_telemLogState = -result;
      if (result == FR_NOT_READY)
        strcpy_P(g_logErrorStr, PSTR("NO DATA CARD"));
      else
        strcpy_P(g_logErrorStr, PSTR("CARD ERROR"));
      return;
    }
  } // while
  g_telemLogState = result;

  // g_logFilename should now be set appropriately.

}

// doTelemLog: Append current telemtry and switch status data to log file
// Called every perMain (gruvin9x.cpp) TODO -- NOT GOOD.
// Should be maximum once a second. This either needs to be configurable or
// be called from the Fr-Sky telemetry decode routines, in event-driven fashion.

// Would be best in-lined as well -- but G++ won't allow that to happen with code that's split across files.
// If we really want it inlined, then we'll need to stick it in its own file (log_inc.cpp) and include it 
// where it's wanted. *shrug*
void doTelemLog()
{
  FRESULT result;

  if (isFunctionActive(FUNC_TELEMLOG)) // if FUNC SWITCH for 'Write log data' is on ...
  {
    // Only appeand/create the log file if it's not already open ...
    if (g_telemLogState<=0)
    {
      result = f_mount(0, &g_FATFS_Obj);
      if (result != FR_OK)
      {
        g_telemLogState = -result;
        beepAgain = result - 1;  // DEBUG -- count out error_number beeps
        beepKey();
      }
      else
      {
        // create new log file using filename set up in initTelemLog()
        result = f_open(&g_oLogFile, logFullPath, FA_OPEN_ALWAYS | FA_WRITE);
        if (result != FR_OK)
        {
          g_telemLogState = -result;
          beepAgain = result - 1; // DEBUG -- count out error_number beeps
          beepKey();
        }
        else
        {
          if (g_oLogFile.fsize == 0) {
            // if data type == Hub TODO
            f_puts("Buffer,RX,TX,A1,A2,Date,Time,Long,Lat,Course,Speed,Alt,BarAlt,"
                "Temp1,Temp2,RPM,Fuel,Volts,AccelX,AccelY,AccelZ,THR,RUD,ELE,IDL0,IDL1,IDL2,AIL,GEA,TRN\n",
                &g_oLogFile);
          }

          f_lseek(&g_oLogFile, g_oLogFile.fsize); // append
          g_telemLogState = 1;
          beepWarn2(); // DEBUG -- tell user the log is open
        }
      }
    }

    if (g_telemLogState>0)
    {
      // TODO here we write logs
      // For now, append 'anything' as a test
      // if data type == Hub
      f_printf(&g_oLogFile, "%d,", frskyStreaming);
      f_printf(&g_oLogFile, "%d,", frskyRSSI[0].value);
      f_printf(&g_oLogFile, "%d,", frskyRSSI[1].value);
      f_printf(&g_oLogFile, "%d,", frskyComputeVolts(frskyTelemetry[0].value, g_model.frsky.channels[0].ratio));
      f_printf(&g_oLogFile, "%d,", frskyComputeVolts(frskyTelemetry[1].value, g_model.frsky.channels[1].ratio));
      f_printf(&g_oLogFile, "%4d-%02d-%02d,", frskyHubData.year+2000, frskyHubData.month, frskyHubData.day);
      f_printf(&g_oLogFile, "%02d:%02d:%02d,", frskyHubData.hour, frskyHubData.min, frskyHubData.sec);
      f_printf(&g_oLogFile, "%03d.%04d%c,", frskyHubData.gpsLongitude_bp, frskyHubData.gpsLongitude_ap,
          frskyHubData.gpsLongitudeEW ? frskyHubData.gpsLongitudeEW : '-');
      f_printf(&g_oLogFile, "%03d.%04d%c,", frskyHubData.gpsLatitude_bp, frskyHubData.gpsLatitude_ap, 
          frskyHubData.gpsLatitudeNS ? frskyHubData.gpsLatitudeNS : '-');
      f_printf(&g_oLogFile, "%03d.%d,", frskyHubData.gpsCourse_bp, frskyHubData.gpsCourse_ap);
      f_printf(&g_oLogFile, "%d.%d,", frskyHubData.gpsSpeed_bp, frskyHubData.gpsSpeed_ap);
      f_printf(&g_oLogFile, "%03d.%d,", frskyHubData.gpsAltitude_bp, frskyHubData.gpsAltitude_ap);
      f_printf(&g_oLogFile, "%d,", frskyHubData.baroAltitude + baroAltitudeOffset);
      f_printf(&g_oLogFile, "%d,", frskyHubData.temperature1);
      f_printf(&g_oLogFile, "%d,", frskyHubData.temperature2);
      f_printf(&g_oLogFile, "%d,", frskyHubData.rpm);
      f_printf(&g_oLogFile, "%d,", frskyHubData.fuelLevel);
      f_printf(&g_oLogFile, "%d,", frskyHubData.volts);
      f_printf(&g_oLogFile, "%d,", frskyHubData.accelX);
      f_printf(&g_oLogFile, "%d,", frskyHubData.accelY);
      f_printf(&g_oLogFile, "%d,", frskyHubData.accelZ);
      f_printf(&g_oLogFile, "%d,", keyState(SW_ThrCt));
      f_printf(&g_oLogFile, "%d,", keyState(SW_RuddDR));
      f_printf(&g_oLogFile, "%d,", keyState(SW_ElevDR));
      f_printf(&g_oLogFile, "%d,", keyState(SW_ID0));
      f_printf(&g_oLogFile, "%d,", keyState(SW_ID1));
      f_printf(&g_oLogFile, "%d,", keyState(SW_ID2));
      f_printf(&g_oLogFile, "%d,", keyState(SW_AileDR));
      f_printf(&g_oLogFile, "%d,", keyState(SW_Gear));
      f_printf(&g_oLogFile, "%d\n", keyState(SW_Trainer));

      // Don't close the log file here. We have 'soft off' available on the v4.1 board. Once
      // that is implemented, it can take care of closing the file, should the radio be
      // powered off before the FUNC SWITCH is turned off.
    }
  }
  else if (g_telemLogState > 0)
  {
    f_close(&g_oLogFile);
    beepWarn2();
    g_telemLogState = 0;
  }
}
