gruvin/gruvin9x/firmware/src/templates.cpp

/*
 * Authors (alphabetical order)
 * - Bertrand Songis <bsongis@gmail.com>
 * - Bryan J. Rentoul (Gruvin) <gruvin@gmail.com>
 *
 * gruvin9x is based on code named er9x by
 * Author - Erez Raviv <erezraviv@gmail.com>, which is in turn
 * was based on the original (and ongoing) project by Thomas Husterer,
 * th9x -- http://code.google.com/p/th9x/
 *
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
 *
 *
 * ============================================================
 * Templates file
 *
 * eccpm
 * crow
 * throttle cut
 * flaperon
 * elevon
 * v-tail
 * throttle hold
 * Aileron Differential
 * Spoilers
 * Snap Roll
 * ELE->Flap
 * Flap->ELE
 *
 *
 *
 * =============================================================
 * Assumptions:
 * All primary channels are per modi12x3
 * Each template added to the end of each channel
 *
 *
 *
 */

#include "gruvin9x.h"
#include "templates.h"

const pm_char stn1[] PROGMEM =  "Simple 4-CH";
const pm_char stn2[] PROGMEM =  "T-Cut";
const pm_char stn3[] PROGMEM =  "V-Tail";
const pm_char stn4[] PROGMEM =  "Elevon\\Delta";
const pm_char stn5[] PROGMEM =  "eCCPM";
const pm_char stn6[] PROGMEM =  "Heli Setup";
const pm_char stn7[] PROGMEM =  "Servo Test";
const pm_char * const n_Templates[] PROGMEM =
{
  stn1,
  stn2,
  stn3,
  stn4,
  stn5,
  stn6,
  stn7
};

MixData* setDest(uint8_t dch)
{
    uint8_t i = 0;
    while ((g_model.mixData[i].destCh<=dch) && (g_model.mixData[i].destCh) && (i<MAX_MIXERS)) i++;
    if(i==MAX_MIXERS) return &g_model.mixData[0];

    memmove(&g_model.mixData[i+1],&g_model.mixData[i],
            (MAX_MIXERS-(i+1))*sizeof(MixData) );
    memset(&g_model.mixData[i],0,sizeof(MixData));
    g_model.mixData[i].destCh = dch;
    return &g_model.mixData[i];
}

void clearMixes()
{
    memset(g_model.mixData,0,sizeof(g_model.mixData)); //clear all mixes
    STORE_MODELVARS;
}

void clearCurves()
{
    memset(g_model.curves5,0,sizeof(g_model.curves5)); //clear all curves
    memset(g_model.curves9,0,sizeof(g_model.curves9)); //clear all curves
}

void setCurve(uint8_t c, const pm_int8_t ar[])
{
    if(c<MAX_CURVE5) //5 pt curve
        for(uint8_t i=0; i<5; i++) g_model.curves5[c][i] = pgm_read_byte(&ar[i]);
    else  //9 pt curve
        for(uint8_t i=0; i<9; i++) g_model.curves9[c-MAX_CURVE5][i] = pgm_read_byte(&ar[i]);
}

void setSwitch(uint8_t idx, uint8_t func, int8_t v1, int8_t v2)
{
    g_model.customSw[idx-1].func = func;
    g_model.customSw[idx-1].v1   = v1;
    g_model.customSw[idx-1].v2   = v2;
}

const pm_int8_t heli_ar1[] PROGMEM = {-100, 20, 50, 70, 90};
const pm_int8_t heli_ar2[] PROGMEM = {90, 70, 50, 70, 90};
const pm_int8_t heli_ar3[] PROGMEM = {-20, -20, 0, 60, 100};
const pm_int8_t heli_ar4[] PROGMEM = {-100, -60, 0, 60, 100};
const pm_int8_t heli_ar5[] PROGMEM = {-100, 0, 0, 0, 100};
void applyTemplate(uint8_t idx)
{
    MixData *md = &g_model.mixData[0];

    //CC(STK)   -> vSTK
    //ICC(vSTK) -> STK
#define ICC(x) icc[(x)-1]
    uint8_t icc[4] = {0};
    for(uint8_t i=1; i<=4; i++) //generate inverse array
        for(uint8_t j=1; j<=4; j++) if(CC(i)==j) icc[j-1]=i;

    switch (idx){
      // Simple 4-Ch
      case (0):
        clearMixes();
        md=setDest(ICC(STK_RUD));  md->srcRaw=CM(STK_RUD);  md->weight=100;
        md=setDest(ICC(STK_ELE));  md->srcRaw=CM(STK_ELE);  md->weight=100;
        md=setDest(ICC(STK_THR));  md->srcRaw=CM(STK_THR);  md->weight=100;
        md=setDest(ICC(STK_AIL));  md->srcRaw=CM(STK_AIL);  md->weight=100;
        break;

      // T-Cut
      case (1):
        md=setDest(ICC(STK_THR));  md->srcRaw=MIX_MAX;  md->weight=-100;  md->swtch=DSW_THR;  md->mltpx=MLTPX_REP;
        break;

      // V-Tail
      case (2):
        md=setDest(ICC(STK_RUD));  md->srcRaw=CM(STK_RUD);  md->weight= 100;
        md=setDest(ICC(STK_RUD));  md->srcRaw=CM(STK_ELE);  md->weight=-100;
        md=setDest(ICC(STK_ELE));  md->srcRaw=CM(STK_RUD);  md->weight= 100;
        md=setDest(ICC(STK_ELE));  md->srcRaw=CM(STK_ELE);  md->weight= 100;
        break;

      // Elevon\\Delta
      case (3):
        md=setDest(ICC(STK_ELE));  md->srcRaw=CM(STK_ELE);  md->weight= 100;
        md=setDest(ICC(STK_ELE));  md->srcRaw=CM(STK_AIL);  md->weight= 100;
        md=setDest(ICC(STK_AIL));  md->srcRaw=CM(STK_ELE);  md->weight= 100;
        md=setDest(ICC(STK_AIL));  md->srcRaw=CM(STK_AIL);  md->weight=-100;
        break;

      // eCCPM
      case (4):
        md=setDest(ICC(STK_ELE));  md->srcRaw=CM(STK_ELE);  md->weight= 72;
        md=setDest(ICC(STK_ELE));  md->srcRaw=CM(STK_THR);  md->weight= 55;
        md=setDest(ICC(STK_AIL));  md->srcRaw=CM(STK_ELE);  md->weight=-36;
        md=setDest(ICC(STK_AIL));  md->srcRaw=CM(STK_AIL);  md->weight= 62;
        md=setDest(ICC(STK_AIL));  md->srcRaw=CM(STK_THR);  md->weight= 55;
        md=setDest(6);             md->srcRaw=CM(STK_ELE);  md->weight=-36;
        md=setDest(6);             md->srcRaw=CM(STK_AIL);  md->weight=-62;
        md=setDest(6);             md->srcRaw=CM(STK_THR);  md->weight= 55;
        break;

      // Heli Setup
      case (5):
        clearMixes();  //This time we want a clean slate
        clearCurves();

        //Set up Mixes
        md=setDest(ICC(STK_AIL));  md->srcRaw=CH(9);   md->weight=  50;
        md=setDest(ICC(STK_AIL));  md->srcRaw=CH(10);  md->weight=-100;
        md=setDest(ICC(STK_AIL));  md->srcRaw=CH(11);  md->weight= 100; md->carryTrim=TRIM_OFF;

        md=setDest(ICC(STK_ELE));  md->srcRaw=CH(9);   md->weight=-100;
        md=setDest(ICC(STK_ELE));  md->srcRaw=CH(11);  md->weight= 100; md->carryTrim=TRIM_OFF;

        md=setDest(ICC(STK_THR));  md->srcRaw=CM(STK_THR);  md->weight= 100; md->swtch=DSW_ID0; md->curve=CV(1); md->carryTrim=TRIM_OFF;
        md=setDest(ICC(STK_THR));  md->srcRaw=CM(STK_THR);  md->weight= 100; md->swtch=DSW_ID1; md->curve=CV(2); md->carryTrim=TRIM_OFF;
        md=setDest(ICC(STK_THR));  md->srcRaw=CM(STK_THR);  md->weight= 110; md->swtch=DSW_ID2; md->curve=CV(2); md->carryTrim=TRIM_OFF;
        md=setDest(ICC(STK_THR));  md->srcRaw=MIX_MAX;      md->weight=-125; md->swtch=DSW_THR;  md->mltpx=MLTPX_REP; md->carryTrim=TRIM_OFF;

        md=setDest(ICC(STK_RUD));  md->srcRaw=CM(STK_RUD); md->weight=100;

        md=setDest(5);  md->srcRaw=MIX_MAX; md->weight= 50; md->swtch=-DSW_GEA; md->carryTrim=TRIM_OFF;
        md=setDest(5);  md->srcRaw=MIX_MAX; md->weight=-50; md->swtch= DSW_GEA; md->carryTrim=TRIM_OFF;
        md=setDest(5);  md->srcRaw=STK_P3;  md->weight= 40; md->carryTrim=TRIM_OFF;

        md=setDest(6);  md->srcRaw=CH(9);   md->weight= -50;
        md=setDest(6);  md->srcRaw=CH(10);  md->weight=-100;
        md=setDest(6);  md->srcRaw=CH(11);  md->weight=-100; md->carryTrim=TRIM_OFF;

        md=setDest(9);  md->srcRaw=CM(STK_ELE);  md->weight= 60;
        md=setDest(10); md->srcRaw=CM(STK_AIL);  md->weight=-52;
        md=setDest(11); md->srcRaw=CM(STK_THR);  md->weight= 70; md->swtch=DSW_ID0; md->curve=CV(3); md->carryTrim=TRIM_OFF;
        md=setDest(11); md->srcRaw=CM(STK_THR);  md->weight= 70; md->swtch=DSW_ID1; md->curve=CV(4); md->carryTrim=TRIM_OFF;
        md=setDest(11); md->srcRaw=CM(STK_THR);  md->weight= 70; md->swtch=DSW_ID2; md->curve=CV(4); md->carryTrim=TRIM_OFF;
        md=setDest(11); md->srcRaw=CM(STK_THR);  md->weight=100; md->swtch=DSW_THR; md->curve=CV(5); md->carryTrim=TRIM_OFF;  md->mltpx=MLTPX_REP;

        //Set up Curves
        setCurve(CURVE5(1), heli_ar1);
        setCurve(CURVE5(2), heli_ar2);
        setCurve(CURVE5(3), heli_ar3);
        setCurve(CURVE5(4), heli_ar4);
        setCurve(CURVE5(5), heli_ar5);
        break;

      // Servo Test
      case (6):
        md=setDest(15); md->srcRaw=CH(16);   md->weight= 100; md->speedUp = 8; md->speedDown = 8;
        md=setDest(16); md->srcRaw=MIX_FULL; md->weight= 110; md->swtch=DSW_SW1;
        md=setDest(16); md->srcRaw=MIX_MAX;  md->weight=-110; md->swtch=DSW_SW2; md->mltpx=MLTPX_REP;
        md=setDest(16); md->srcRaw=MIX_MAX;  md->weight= 110; md->swtch=DSW_SW3; md->mltpx=MLTPX_REP;

        setSwitch(1,CS_LESS,CH(15),CH(16));
        setSwitch(2,CS_VPOS,CH(15),   105);
        setSwitch(3,CS_VNEG,CH(15),  -105);
        break;


    default:
        break;

    }

    STORE_MODELVARS;
}
