gruvin/gruvin9x/firmware/src/frsky.h

/*
 * Authors (alphabetical order)
 * - Bertrand Songis <bsongis@gmail.com>
 * - Bryan J. Rentoul (Gruvin) <gruvin@gmail.com>
 *
 * Original contributors
 * - Philip Moss Adapted first frsky functions from jeti.cpp code by 
 * - Karl Szmutny <shadow@privy.de> 
 *
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
 */

#ifndef FRSKY_H
#define FRSKY_H

#define FRSKY_RX_PACKET_SIZE 19
#define FRSKY_TX_PACKET_SIZE 12

#include <inttypes.h>

// .20 seconds
#define FRSKY_TIMEOUT10ms 20

enum AlarmLevel {
  alarm_off = 0,
  alarm_yellow = 1,
  alarm_orange = 2,
  alarm_red = 3
};

#define ALARM_GREATER(channel, alarm) ((g_model.frsky.channels[channel].alarms_greater >> alarm) & 1)
#define ALARM_LEVEL(channel, alarm) ((g_model.frsky.channels[channel].alarms_level >> (2*alarm)) & 3)

struct FrskyData {
  uint8_t value;
  uint8_t min;
  uint8_t max;
  void set(uint8_t value);
};

#if defined(FRSKY_HUB)
struct FrskyHubData {
  int16_t  gpsAltitude_bp;   // before punct
  int16_t  temperature1;     // -20 .. 250 deg. celcius
  uint16_t rpm;              // 0..60,000 revs. per minute
  uint16_t fuelLevel;        // 0, 25, 50, 75, 100 percent
  int16_t  temperature2;     // -20 .. 250 deg. celcius
  uint16_t volts;            // 1/500V increments (0..4.2V)
  int16_t  gpsAltitude_ap;   // after punct
  uint16_t baroAltitude;     // 0..9,999 meters
  uint16_t gpsSpeed_bp;      // before punct
  uint16_t gpsLongitude_bp;  // before punct
  uint16_t gpsLatitude_bp;   // before punct
  uint16_t gpsCourse_bp;     // before punct (0..359.99 deg. -- seemingly 2-decimal precision)
  uint8_t  day;
  uint8_t  month;
  uint16_t year;
  uint8_t  hour;
  uint8_t  min;
  uint16_t sec;
  uint16_t gpsSpeed_ap;
  uint16_t gpsLongitude_ap;
  uint16_t gpsLatitude_ap;
  uint16_t gpsCourse_ap;
  uint16_t gpsLongitudeEW;   // East/West
  uint16_t gpsLatitudeNS;    // North/South
  int16_t  accelX;           // 1/256th gram (-8g ~ +8g)
  int16_t  accelY;           // 1/256th gram (-8g ~ +8g)
  int16_t  accelZ;           // 1/256th gram (-8g ~ +8g)
};
extern FrskyHubData frskyHubData;
extern int16_t baroAltitudeOffset;
#elif defined(WS_HOW_HIGH)
struct FrskyHubData {
  uint16_t baroAltitude;     // 0..9,999 meters
};
extern FrskyHubData frskyHubData;
extern int16_t baroAltitudeOffset;
#endif

// Global Fr-Sky telemetry data variables
extern uint8_t frskyStreaming; // >0 (true) == data is streaming in. 0 = nodata detected for some time
extern uint8_t frskyUsrStreaming;

#define SEND_MODEL_ALARMS 4
#define SEND_RSSI_ALARMS  (SEND_MODEL_ALARMS + 2)
extern uint8_t FrskyAlarmSendState;

extern FrskyData frskyTelemetry[2];
extern FrskyData frskyRSSI[2];
extern uint8_t frskyRxBufferIn;
extern uint8_t frskyRxBufferOut;
extern uint8_t frskyUserDataIn;
extern uint8_t frskyUserDataOut;

extern uint8_t frskyTxBuffer[FRSKY_TX_PACKET_SIZE];
extern uint8_t frskyTxBufferCount;

extern uint16_t frskyComputeVolts(uint8_t rawADC, uint16_t ratio, uint8_t decimals=1); 
extern void frskyPutAValue(uint8_t x, uint8_t y, uint8_t channel, uint8_t value, uint8_t mode = 0);

void FRSKY_Init(void);
void FRSKY10mspoll(void);

inline void FRSKY_setModelAlarms(void)
{
  FrskyAlarmSendState = SEND_MODEL_ALARMS;
}

bool FRSKY_alarmRaised(uint8_t idx);

void resetTelemetry();

extern double distance(double lat1, double lon1, double lat2, double lon2);

#endif
