gruvin/gruvin9x/firmware/src/stack-monitor.cpp

#ifndef SIMU

#include <avr/wdt.h>

void StackPaint(void) __attribute__ ((naked)) __attribute__ ((section (".init1")));

void StackPaint(void)
{
  wdt_reset();
  wdt_disable();
#if 0
  uint8_t *p = &_end;

  while(p <= &__stack)
  {
    *p = STACK_CANARY;
    p++;
  }
#else
  __asm volatile ("    ldi r30,lo8(_end)\n"
      "    ldi r31,hi8(_end)\n"
      "    ldi r24,lo8(0xc5)\n" /* STACK_CANARY = 0xc5 */
      "    ldi r25,hi8(__stack)\n"
      "    rjmp .cmp\n"
      ".loop:\n"
      "    st Z+,r24\n"
      ".cmp:\n"
      "    cpi r30,lo8(__stack)\n"
      "    cpc r31,r25\n"
      "    brlo .loop\n"
      "    breq .loop"::);
#endif
} 

#endif
